Esterelieasy/EstereliEasy-Manual/Mídia/EstereliEasy5.jpeg

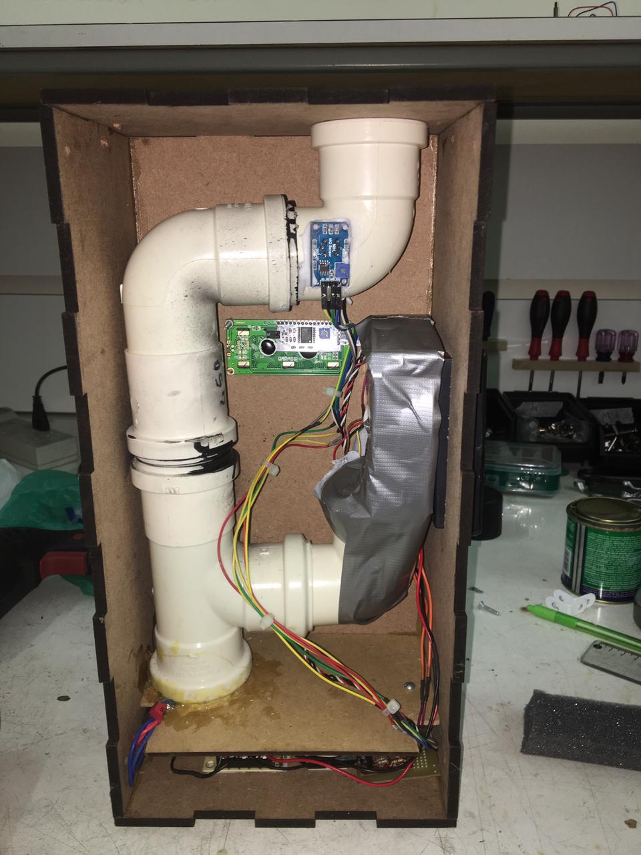
Mídia/EstereliEasy5.jpeg
